imvovas/StairLights/photos/IMG_20190717_142647601.jpg

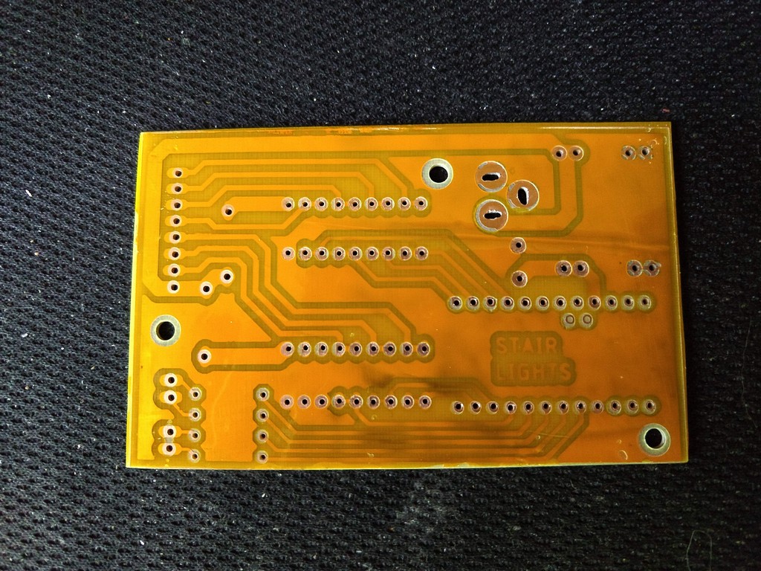
photos/IMG_20190717_142647601.jpg
