imvovas/StairLights/photos/IMG_20190717_154605497.jpg

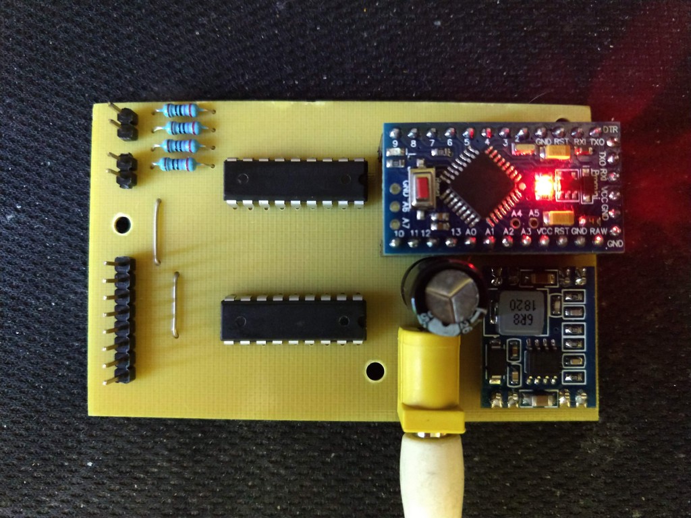
photos/IMG_20190717_154605497.jpg
