imvovas/StairLights/photos/IMG_20190717_155624856.jpg

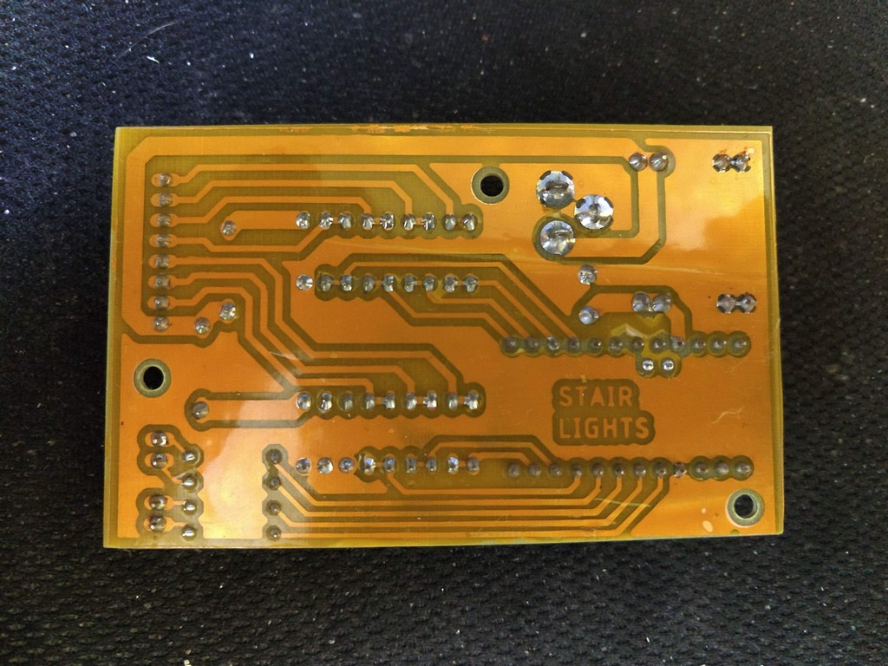
photos/IMG_20190717_155624856.jpg
