imvovas/StairLights/photos/IMG_20190718_221329334.jpg

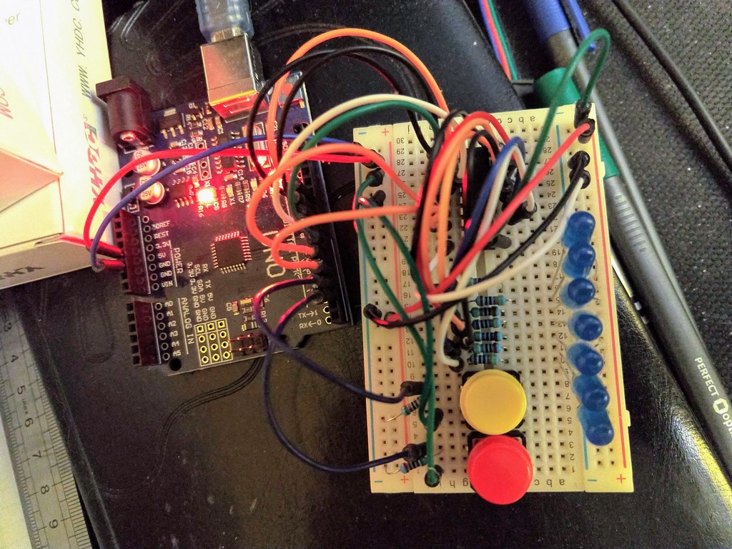
photos/IMG_20190718_221329334.jpg
