imvovas/StairLights/photos/IMG_20190719_140538776.jpg

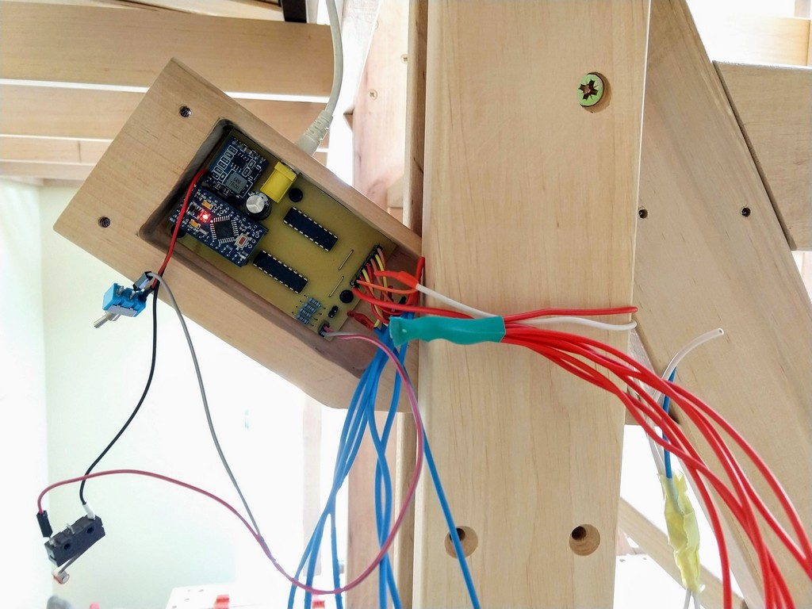
photos/IMG_20190719_140538776.jpg
