imvovas/StairLights/photos/IMG_20190719_143642327.jpg

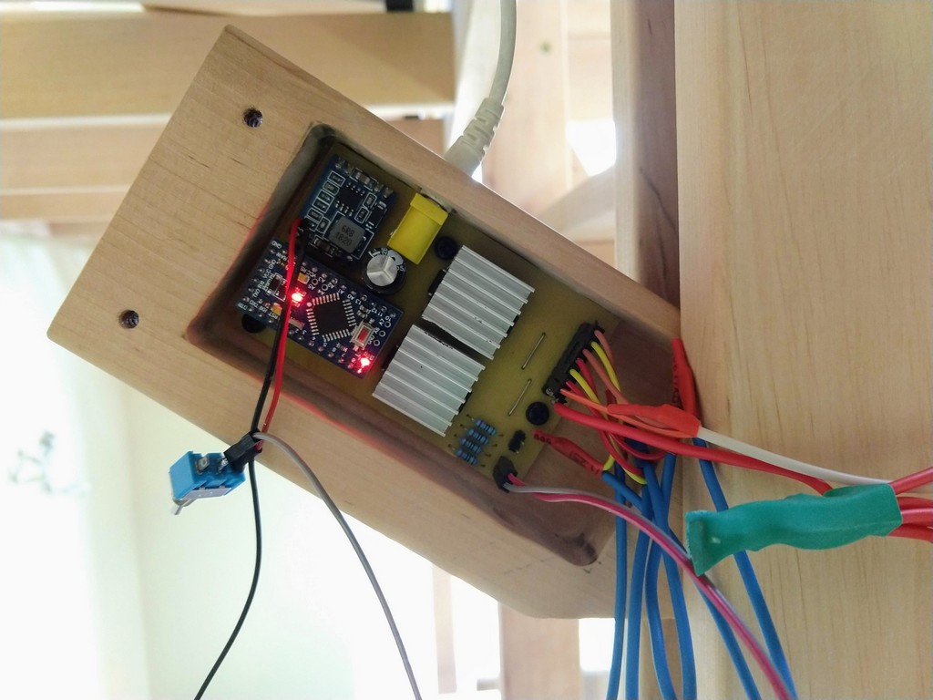
photos/IMG_20190719_143642327.jpg
