imvovas/StairLights/photos/IMG_20190805_171652560.jpg

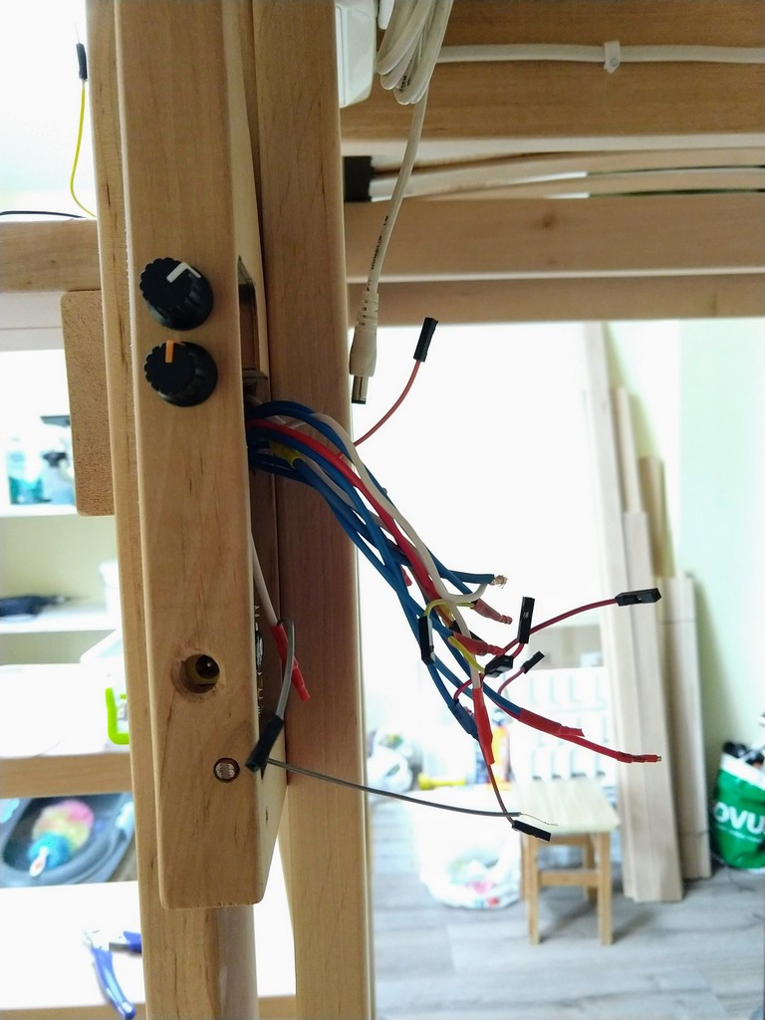
photos/IMG_20190805_171652560.jpg
