imvovas/StairLights/photos/IMG_20200604_133657413.jpg

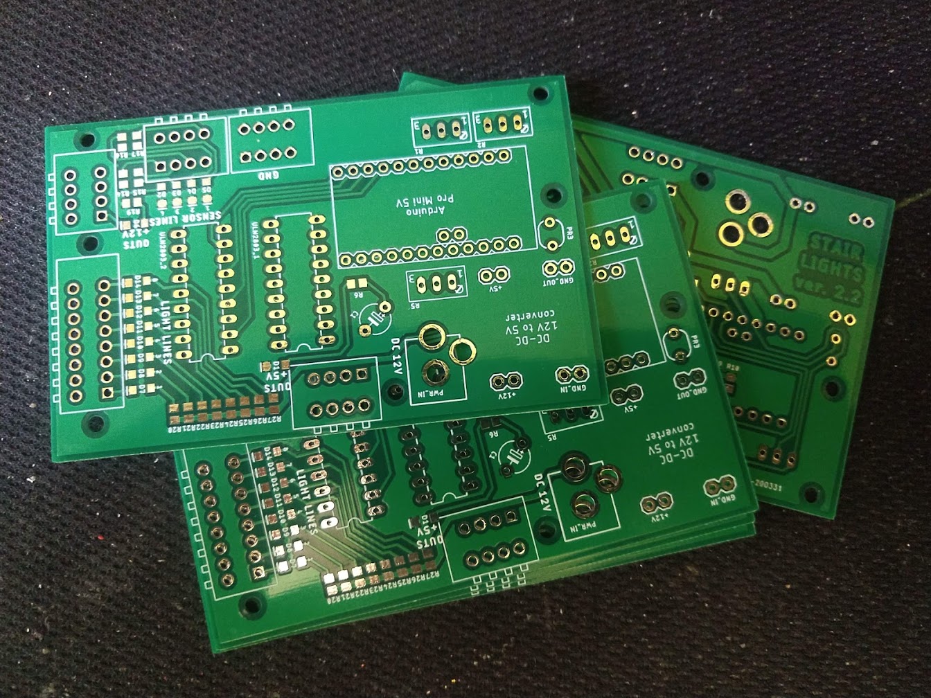
photos/IMG_20200604_133657413.jpg
