imvovas/StairLights/photos/IMG_20200605_112552456.jpg

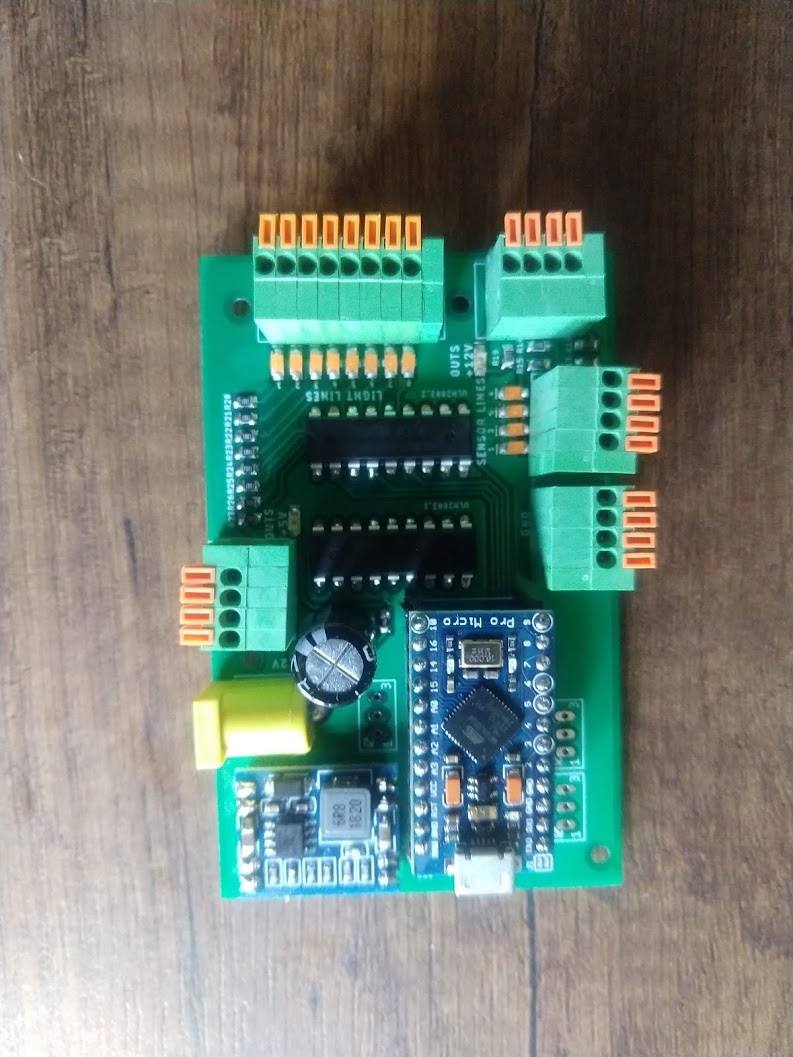
photos/IMG_20200605_112552456.jpg
