imvovas/StairLights/photos/IMG_20200605_112616787.jpg

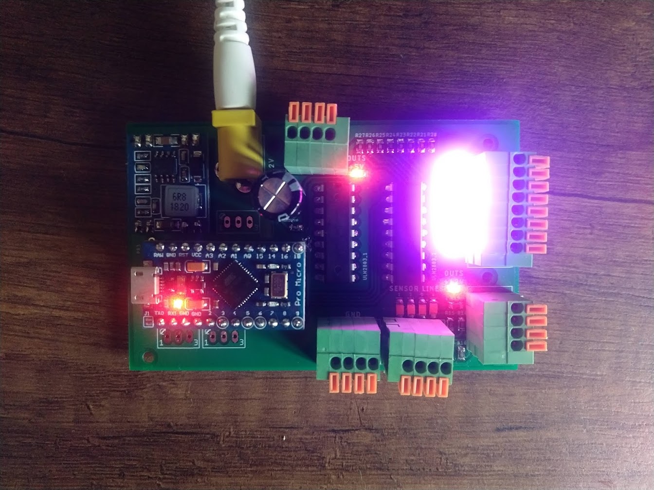
photos/IMG_20200605_112616787.jpg
