imvovas/StairLights/photos/IMG_20200605_113039041.jpg

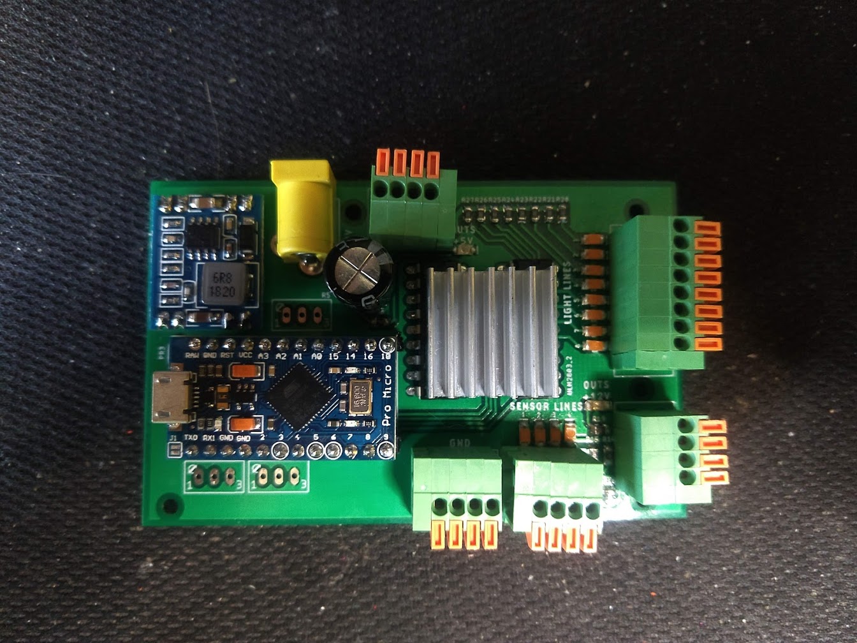
photos/IMG_20200605_113039041.jpg
