imvovas/StairLights/photos/IMG_20200605_150728401.jpg

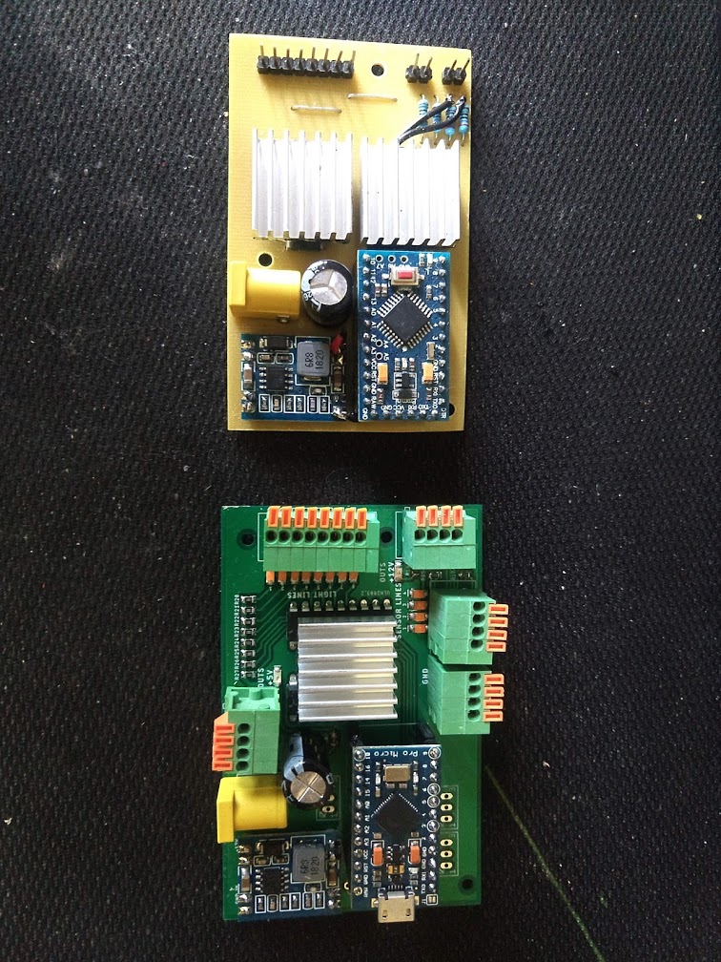
photos/IMG_20200605_150728401.jpg
